WholeWheatOrange/OHEK-80/kicad/void_switch_kicad/assets/images/add_footprint_path2.png

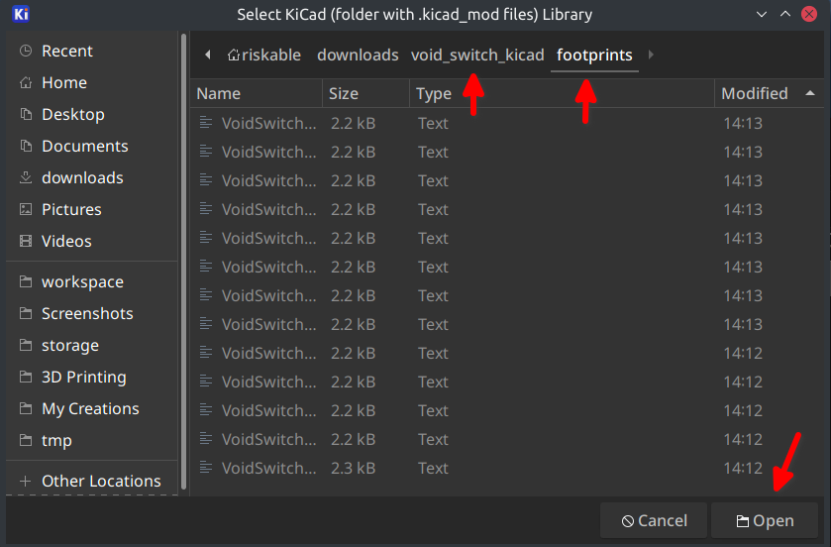
kicad/void_switch_kicad/assets/images/add_footprint_path2.png
